DonBower/HamGoBox/Box/Front-Panel.graffle/image1.jpg

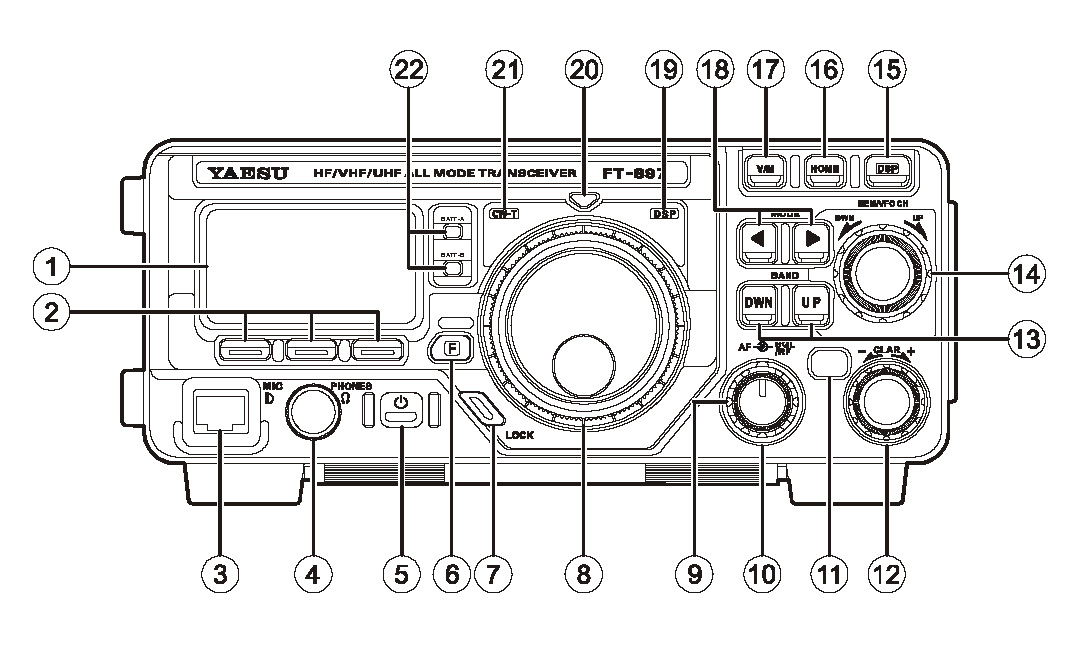
Box/Front-Panel.graffle/image1.jpg
