DonBower/HamGoBox/fldigi/images/fldigi.config.soundcard.devices.png

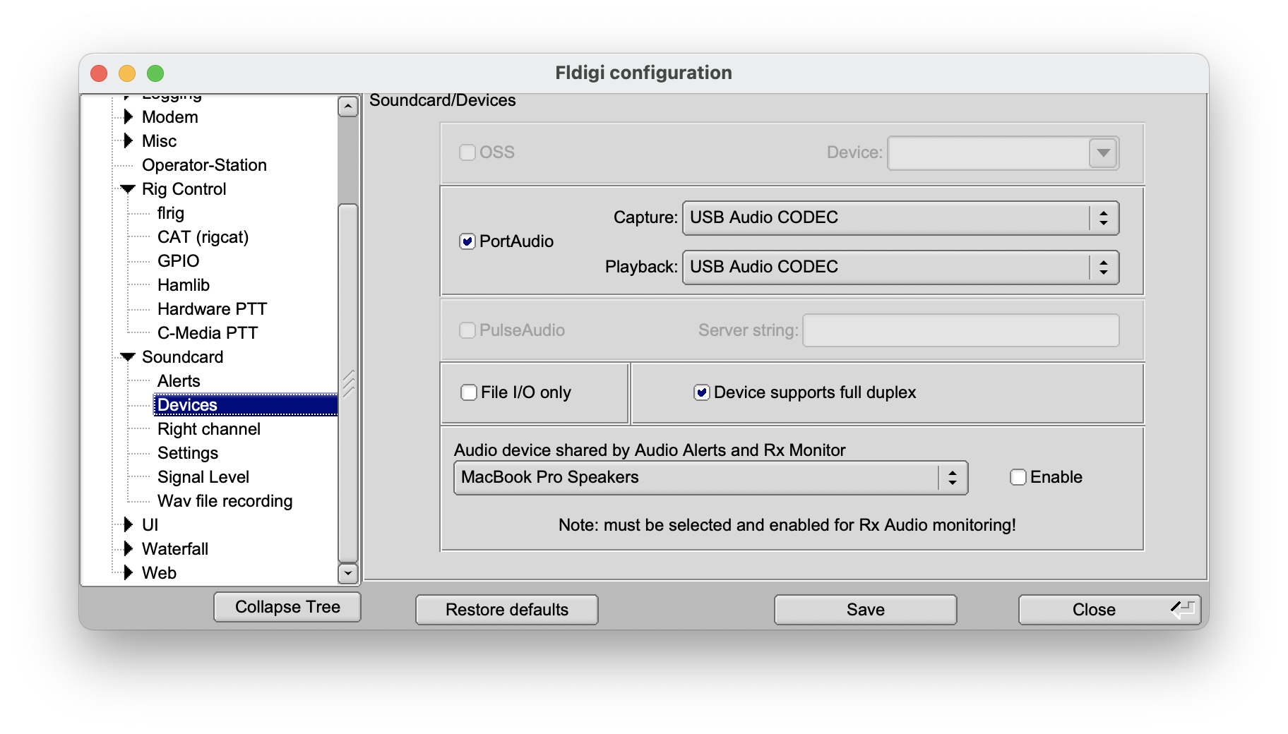
fldigi/images/fldigi.config.soundcard.devices.png
