DonBower/HamGoBox/fldigi/images/fldigi.configure.operatior-station.png

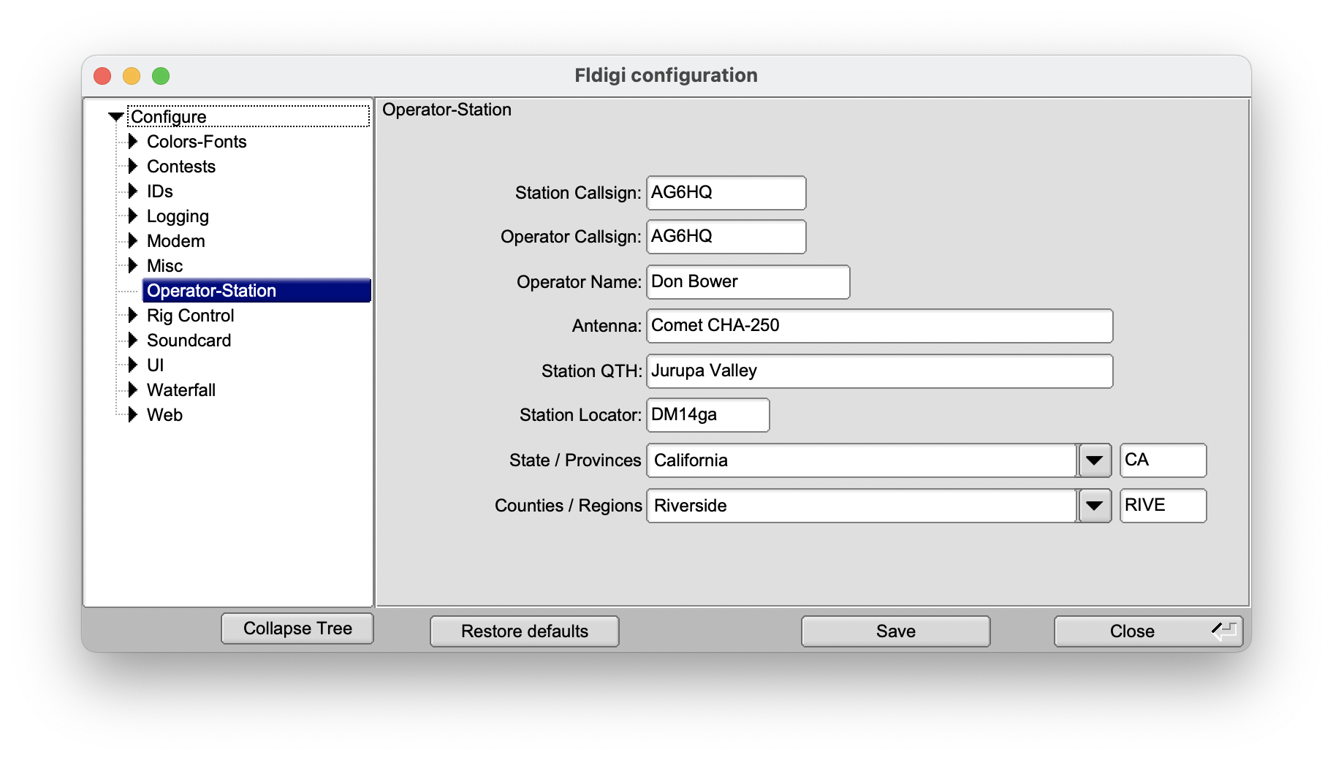
fldigi/images/fldigi.configure.operatior-station.png
