DonBower/HamGoBox/fldigi/images/fldigi.configure.rig-control.flrig2.png

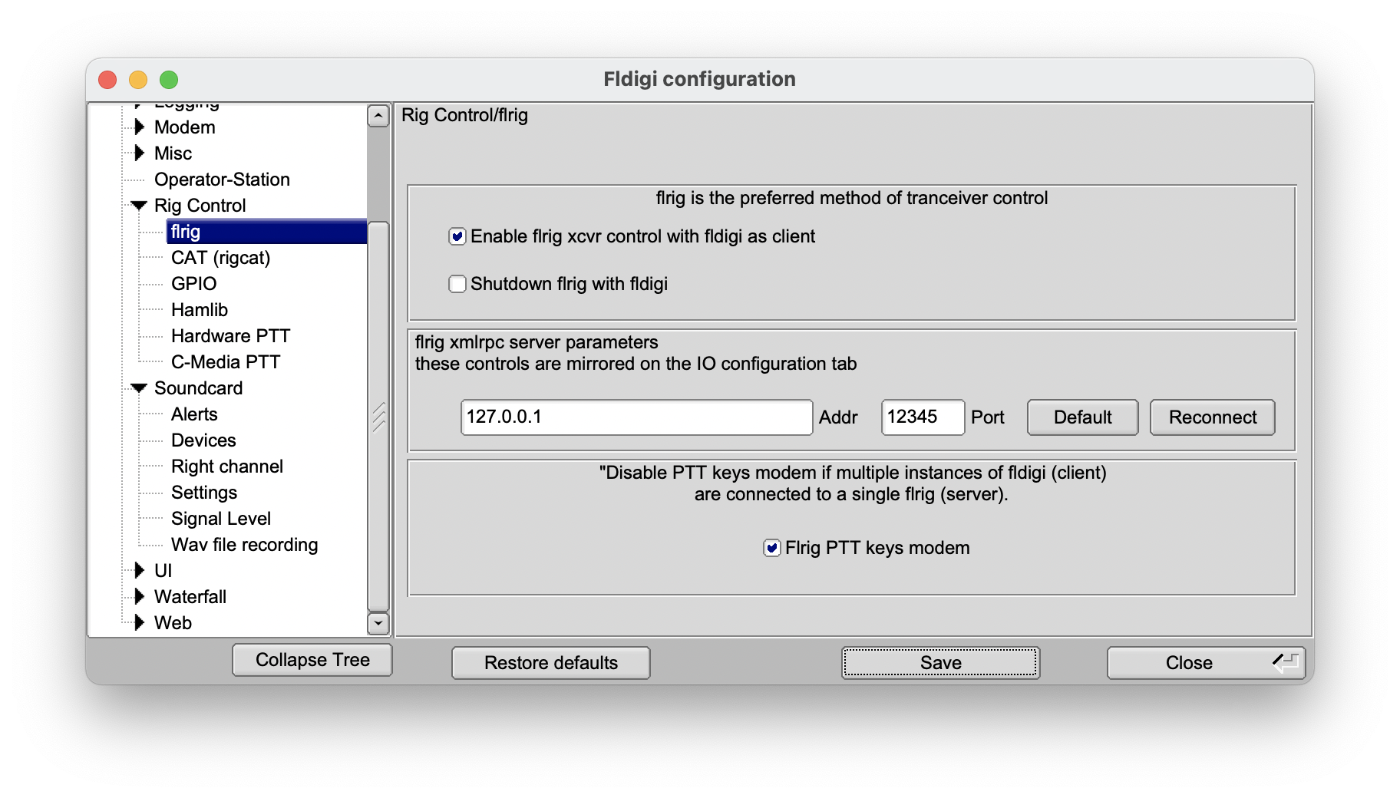
fldigi/images/fldigi.configure.rig-control.flrig2.png
