DonBower/HamGoBox/fldigi/images/fldigi.console.no-waterfall.png

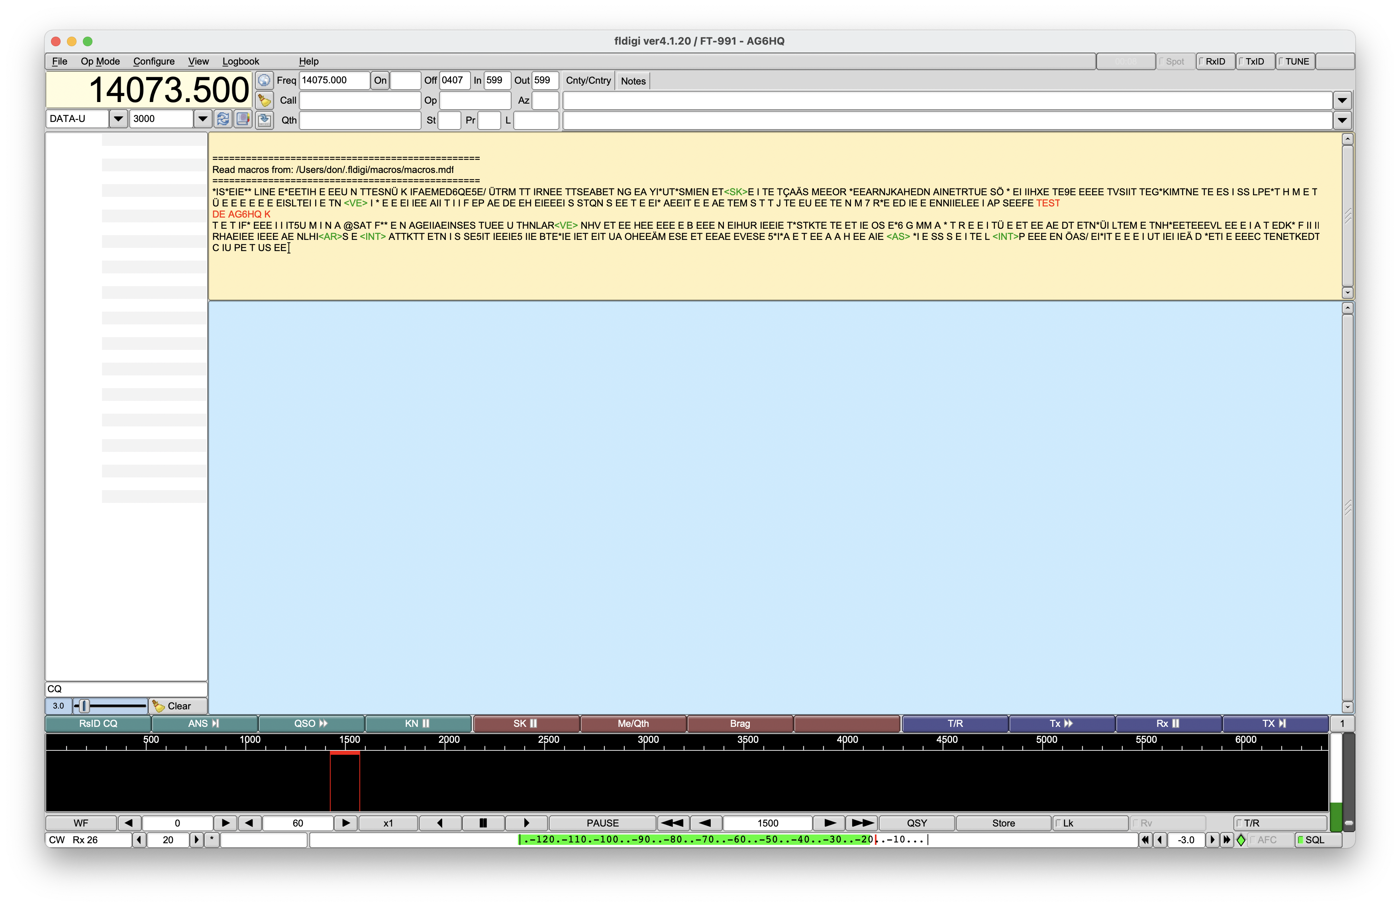
fldigi/images/fldigi.console.no-waterfall.png
