DonBower/HamGoBox/fldigi/images/fldigi.console.vfo.png

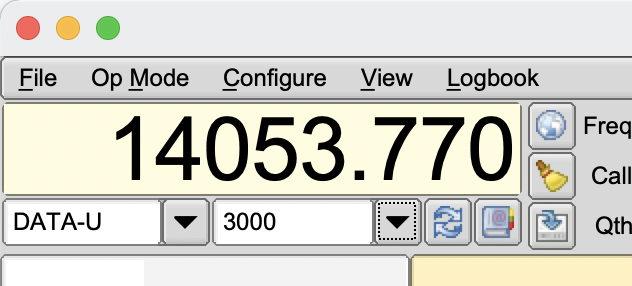
fldigi/images/fldigi.console.vfo.png
