DonBower/HamGoBox/fldigi/images/flrig.configure.poll.png

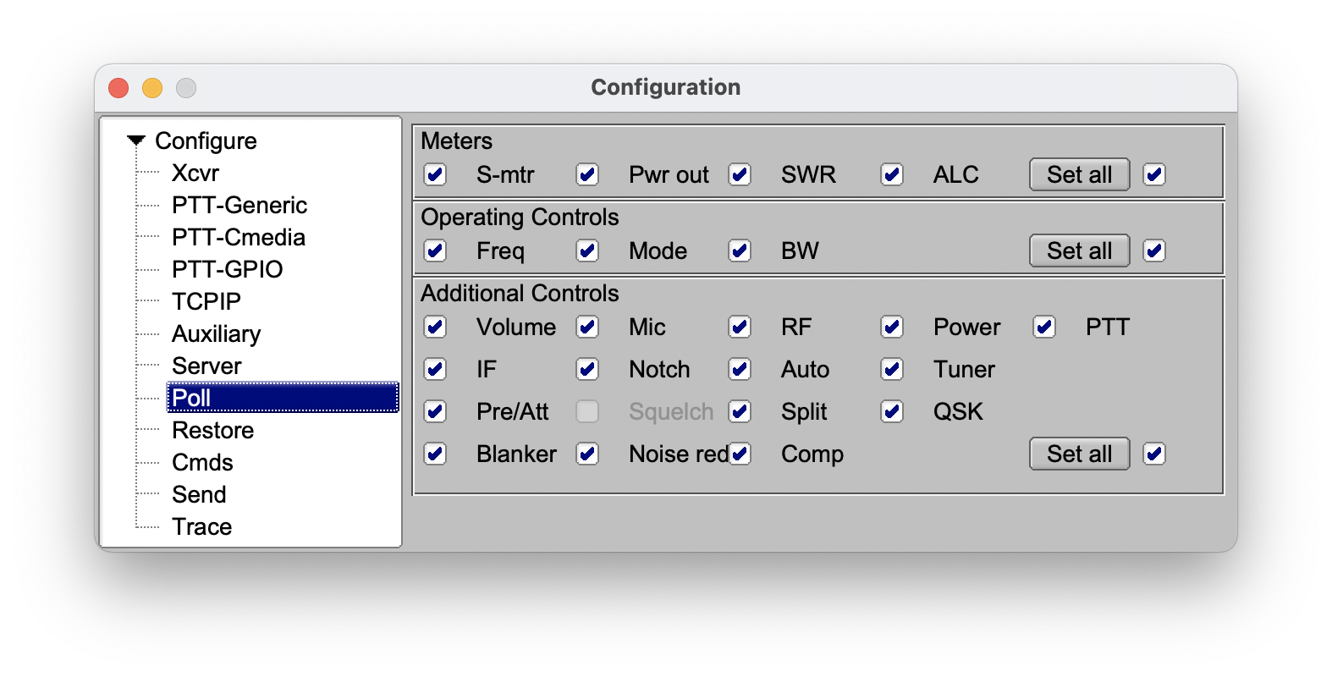
fldigi/images/flrig.configure.poll.png
