DonBower/HamGoBox/fldigi/images/FT991DU.jpeg

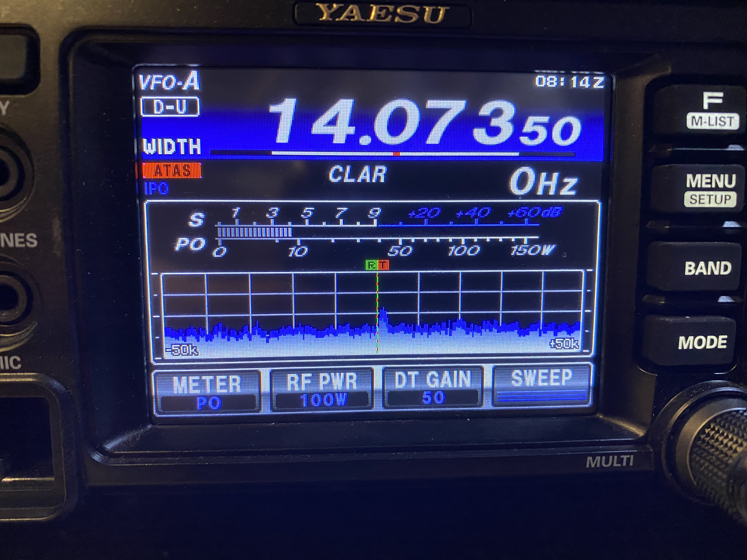
fldigi/images/FT991DU.jpeg
