DonBower/HamGoBox/Images/1UPanel.jpg

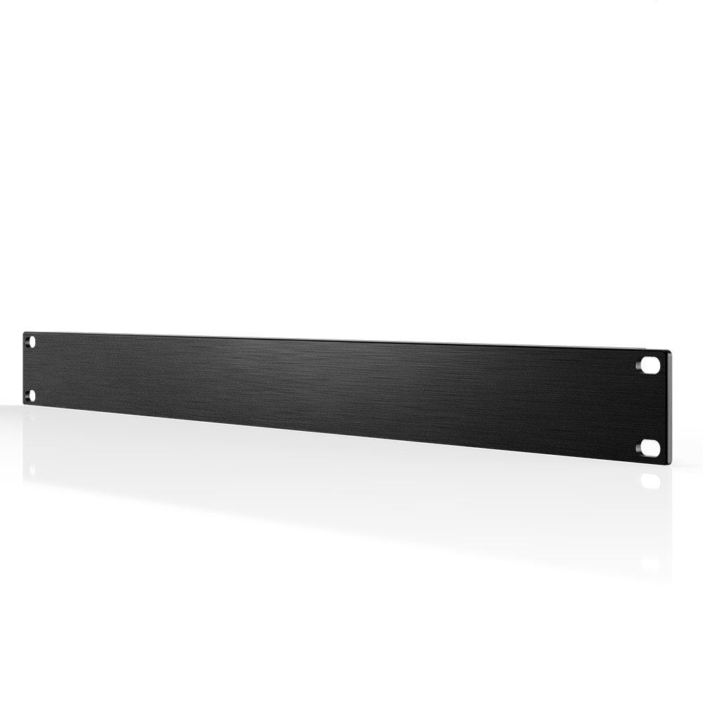
Images/1UPanel.jpg
