DonBower/HamGoBox/Images/Block Diagram.png

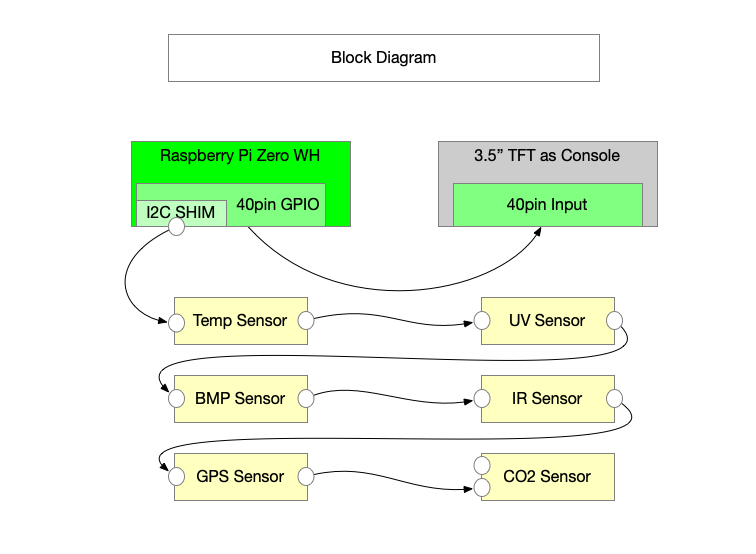
Images/Block Diagram.png
