DonBower/HamGoBox/Images/FT-897DSmall.jpg

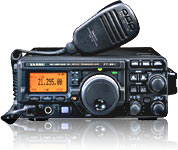
Images/FT-897DSmall.jpg
