DonBower/HamGoBox/Images/GatorBox.jpg

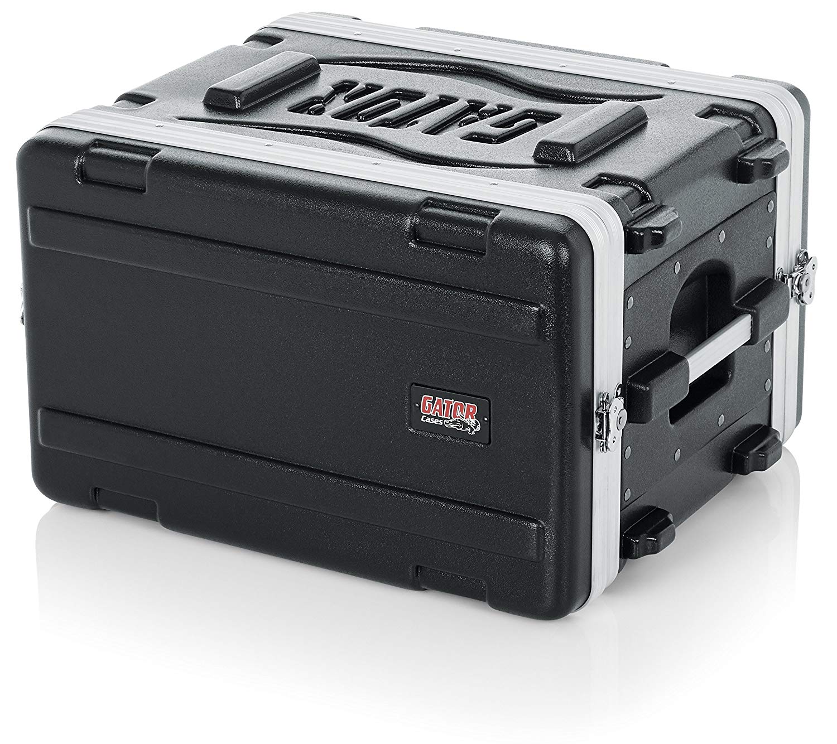
Images/GatorBox.jpg
