DonBower/HamGoBox/Images/IMG_0613.jpeg

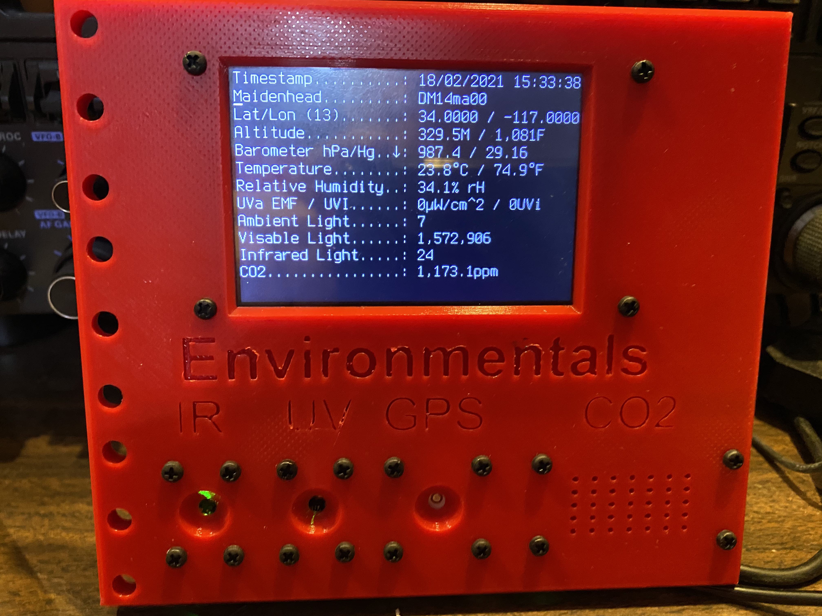
Images/IMG_0613.jpeg
