DonBower/HamGoBox/Images/IMG_0614.jpeg

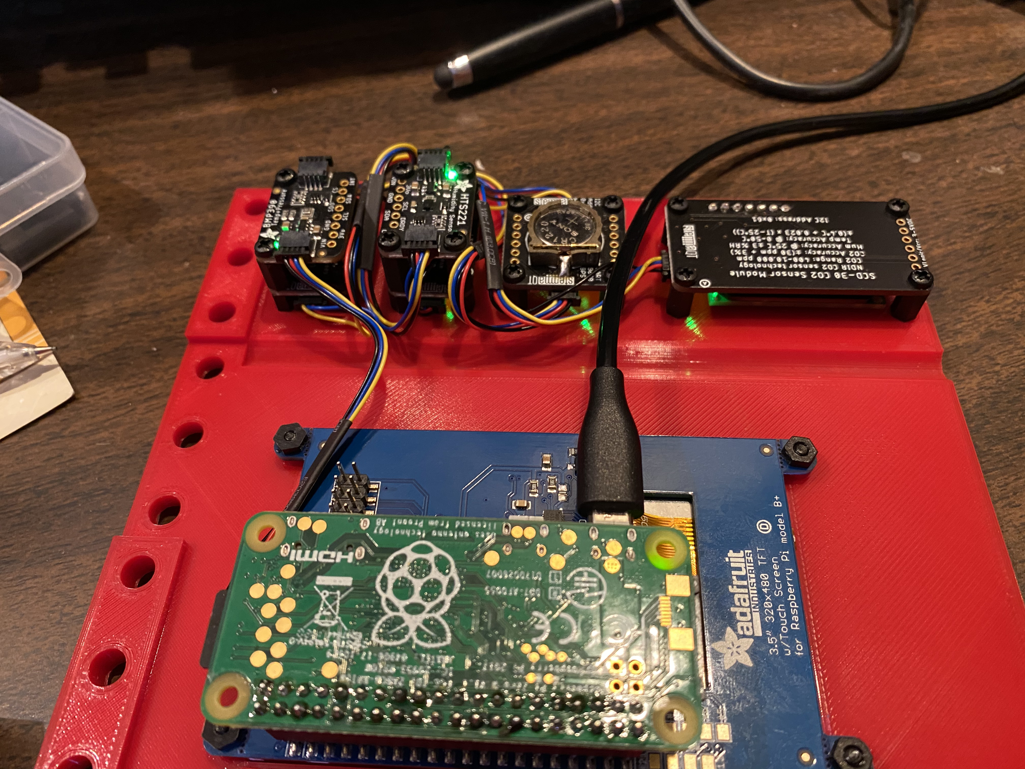
Images/IMG_0614.jpeg
