DonBower/HamGoBox/Images/IMG_0615.jpeg

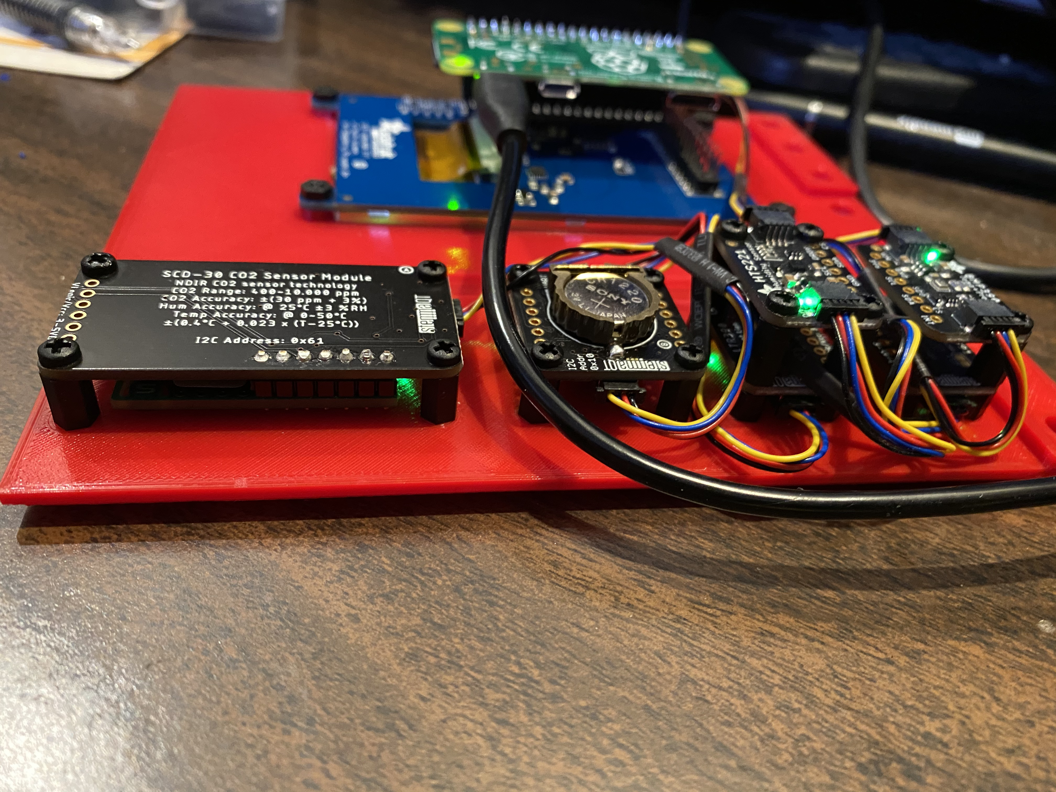
Images/IMG_0615.jpeg
