DonBower/HamGoBox/Images/IMG_0616.jpeg

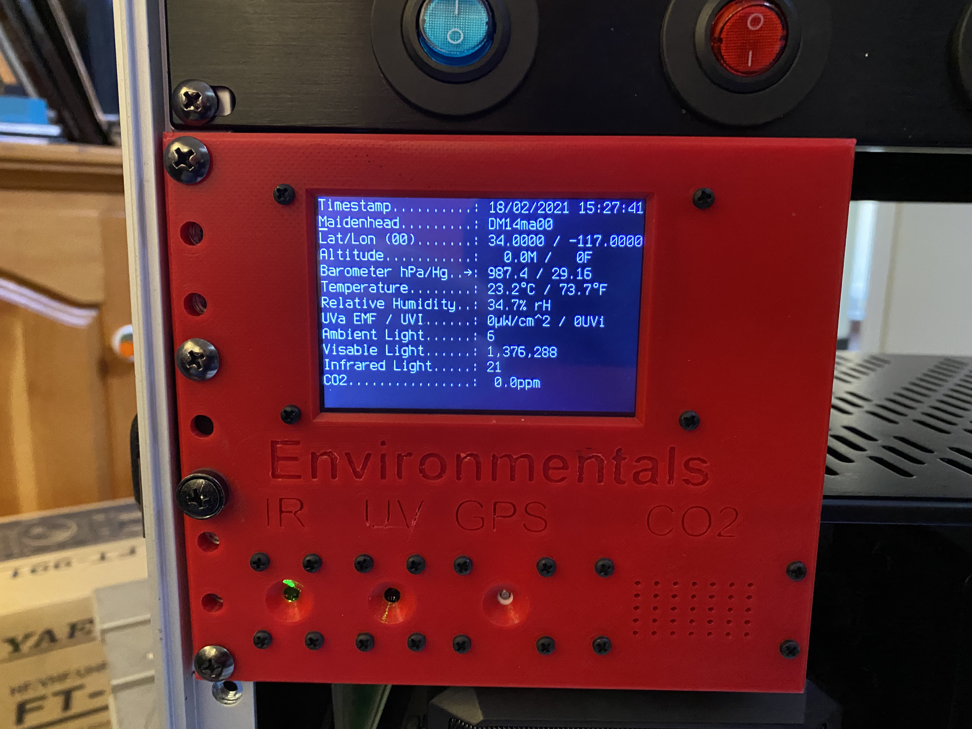
Images/IMG_0616.jpeg
