DonBower/HamGoBox/Images/IMG_0617.jpeg

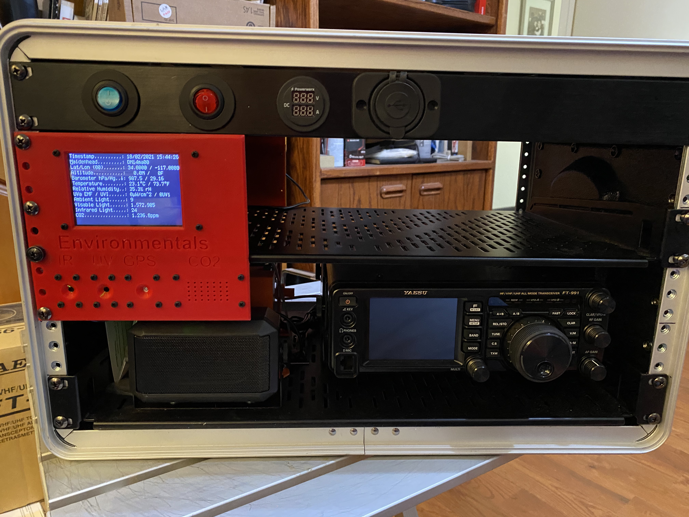
Images/IMG_0617.jpeg
