DonBower/HamGoBox/Images/IMG_0618.jpeg

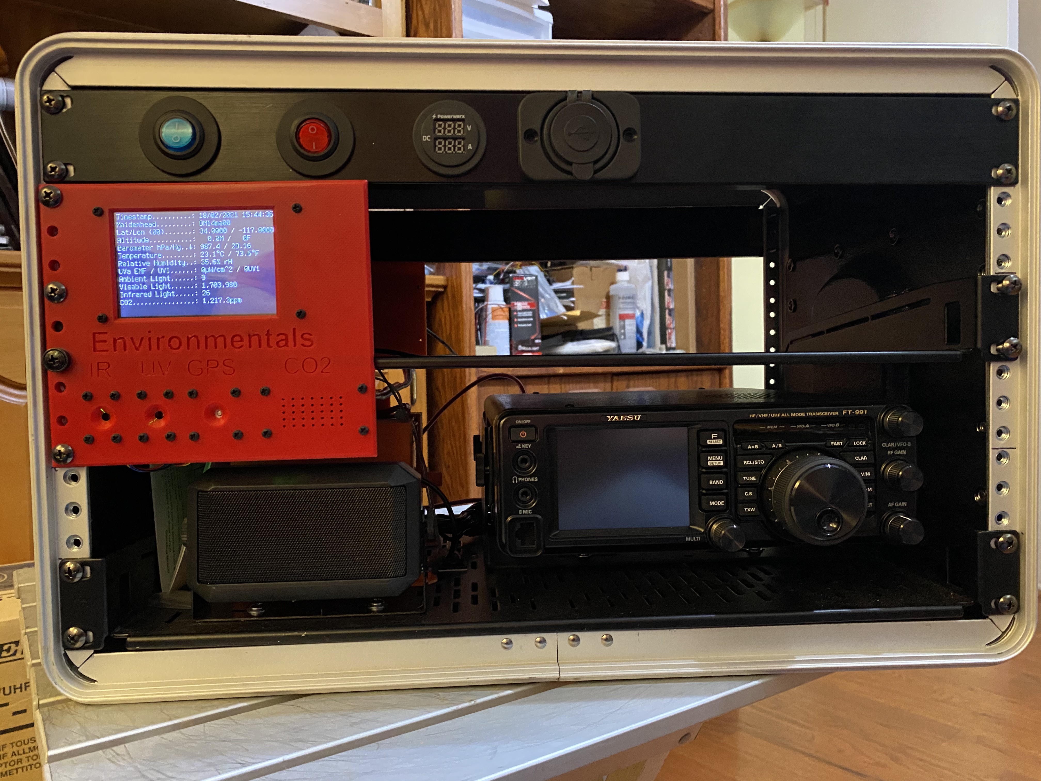
Images/IMG_0618.jpeg
