DonBower/HamGoBox/Images/Interfacing Options.png

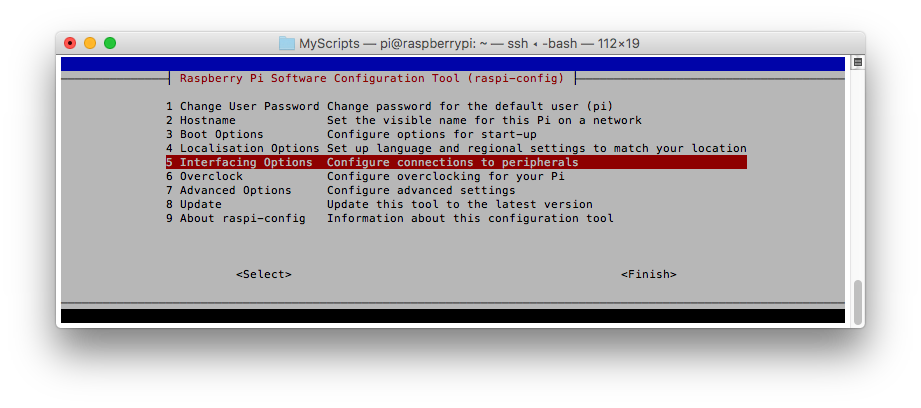
Images/Interfacing Options.png
