DonBower/HamGoBox/Images/monitor.jpg

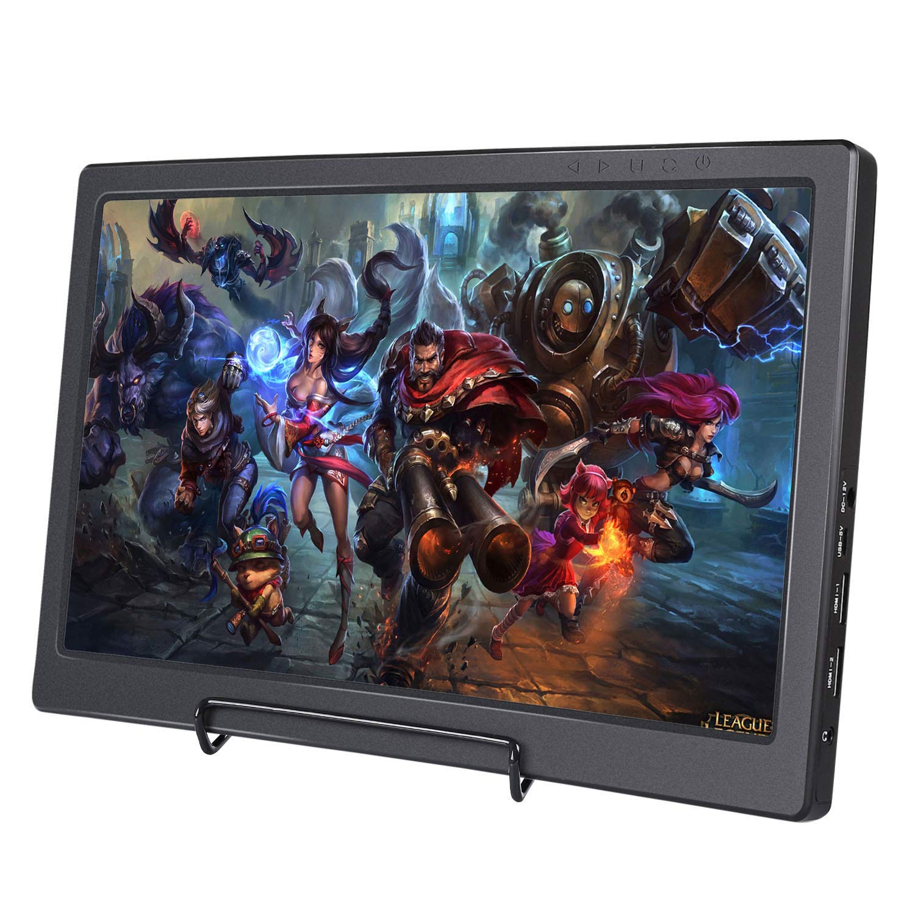
Images/monitor.jpg
