DonBower/HamGoBox/Images/P2 Enable SSH.png

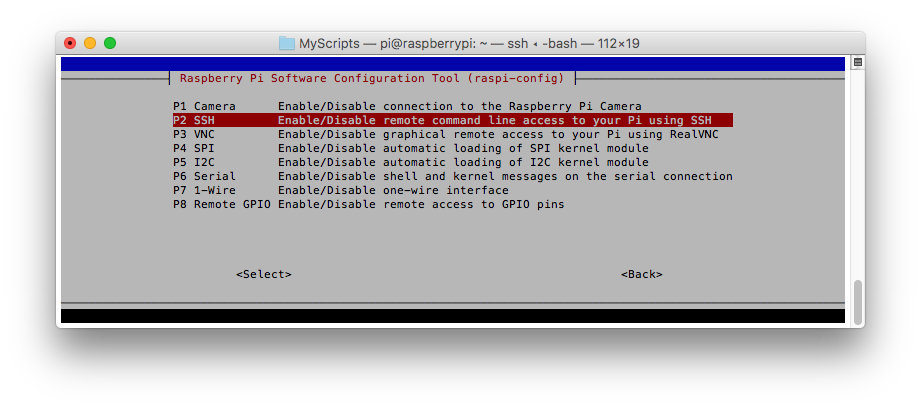
Images/P2 Enable SSH.png
