DonBower/HamGoBox/Images/QTSHIM.jpg

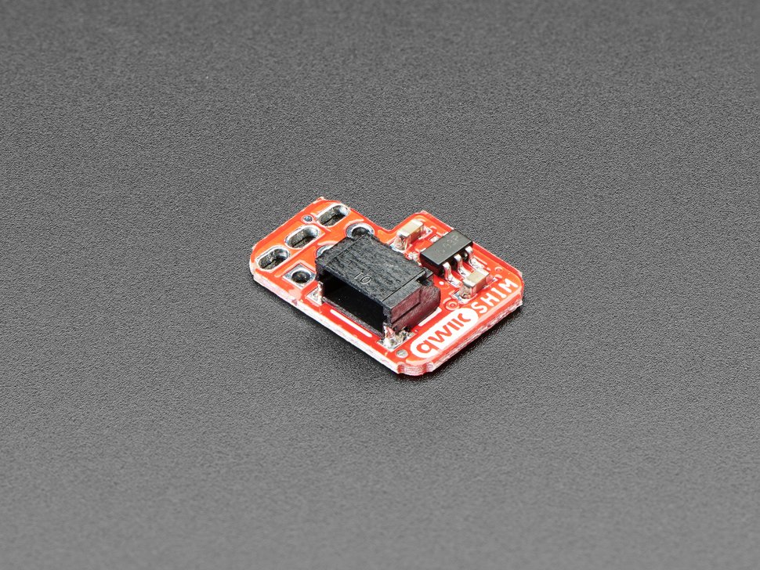
Images/QTSHIM.jpg
