DonBower/HamGoBox/Images/RaspberryPi.jpg

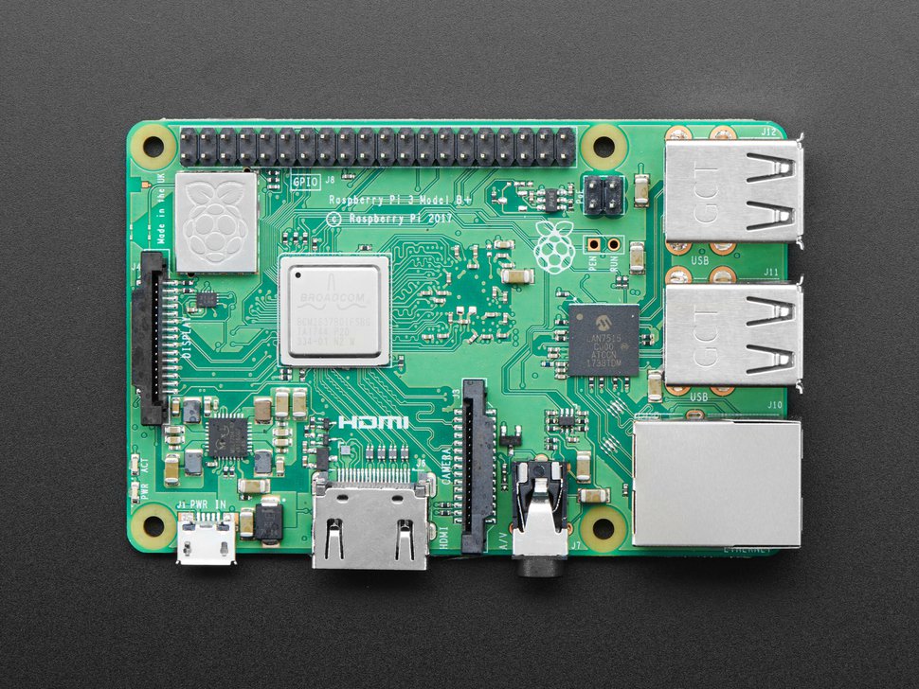
Images/RaspberryPi.jpg
