DonBower/HamGoBox/Images/RaspberryPiSmall.jpg

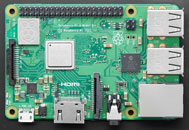
Images/RaspberryPiSmall.jpg
