DonBower/HamGoBox/Images/SelectWiFi.png

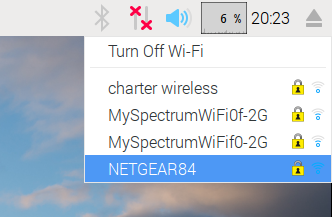
Images/SelectWiFi.png
