DonBower/HamGoBox/Images/WMRPnP.jpg

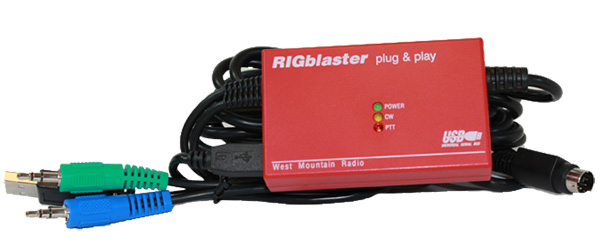
Images/WMRPnP.jpg
