DonBower/HamGoBox/SCD30/simpleTest.py

import time
import board
import busio
import adafruit_scd30

i2c = busio.I2C(board.SCL, board.SDA)
scd = adafruit_scd30.SCD30(i2c)

while True:
    # since the measurement interval is long (2+ seconds) we check for new data before reading
    # the values, to ensure current readings.
    time.sleep(0.5)
    if scd.data_available:
        print("Data Available!")
        print("CO2:", scd.eCO2, "PPM")
        print("Temperature:", scd.temperature, "degrees C")
        print("Humidity:", scd.relative_humidity, "%%rH")
        print("")
        print("Waiting for new data...")
        print("")
